j0ono0/handheld_game_console_prototype_01/arduino_game/resources.cpp

#include "resources.h"

const uint8_t terrain_1[] = {
	1, 1, 1, 1, 1, 1, 1, 1, 1, 1, 1, 1, 1, 1, 1, 1, 1, 1, 1, 1, 1, 1, 1, 1, 1, 1, 1, 1, 1, 1, 1, 1, 1, 1, 1, 1, 1, 1, 1, 1,
	1, 1, 1, 1, 1, 1, 1, 1, 1, 1, 1, 1, 1, 1, 1, 1, 1, 1, 1, 1, 1, 1, 1, 1, 1, 1, 1, 1, 1, 1, 1, 1, 1, 1, 1, 1, 1, 1, 1, 1,
	1, 1, 1, 1, 1, 1, 1, 1, 1, 1, 1, 1, 1, 1, 1, 1, 1, 1, 1, 1, 1, 1, 1, 1, 1, 1, 1, 1, 1, 1, 1, 1, 1, 1, 1, 1, 1, 1, 1, 1,
	1, 1, 1, 1, 1, 1, 1, 1, 1, 1, 1, 1, 1, 1, 1, 1, 1, 1, 1, 1, 1, 1, 1, 1, 1, 1, 1, 1, 1, 1, 1, 1, 1, 1, 1, 1, 1, 1, 1, 1,
	1, 1, 1, 1, 1, 1, 1, 1, 1, 1, 1, 1, 1, 1, 1, 1, 1, 1, 1, 1, 1, 1, 1, 1, 1, 1, 1, 1, 1, 1, 1, 1, 1, 1, 1, 1, 1, 1, 1, 1,
	1, 1, 1, 1, 1, 1, 1, 1, 1, 1, 1, 1, 1, 1, 1, 1, 1, 1, 1, 1, 1, 1, 1, 1, 1, 1, 1, 1, 1, 1, 1, 1, 1, 1, 1, 1, 1, 1, 1, 1,
	1, 1, 1, 1, 1, 1, 1, 1, 1, 1, 1, 1, 1, 1, 1, 1, 1, 1, 1, 1, 1, 1, 1, 1, 1, 1, 1, 1, 1, 1, 1, 1, 1, 1, 1, 1, 1, 1, 1, 1,
	1, 1, 1, 1, 1, 1, 1, 1, 1, 1, 1, 1, 1, 1, 1, 1, 1, 1, 1, 1, 1, 1, 1, 1, 1, 1, 1, 1, 1, 1, 1, 1, 1, 1, 1, 1, 1, 1, 1, 1,
	1, 1, 1, 1, 1, 1, 1, 1, 1, 1, 1, 28, 34, 34, 34, 34, 34, 34, 34, 34, 24, 1, 1, 1, 1, 1, 1, 28, 34, 34, 34, 34, 34, 34, 24, 1, 1, 1, 1, 1,
	1, 1, 1, 1, 1, 1, 1, 1, 1, 1, 1, 28, 13, 13, 13, 13, 13, 13, 13, 13, 29, 1, 1, 1, 1, 1, 1, 28, 13, 13, 13, 13, 13, 13, 29, 1, 1, 1, 1, 1,
	1, 1, 1, 1, 1, 1, 1, 1, 1, 1, 1, 28, 13, 13, 13, 13, 13, 13, 13, 13, 29, 1, 1, 28, 34, 34, 34, 33, 13, 13, 13, 13, 13, 13, 29, 1, 1, 1, 1, 1,
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
	1, 1, 1, 1, 1, 1, 1, 1, 
	1, 1, 1, 1, 1, 1, 1, 1, 
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
};


const Entity entities_01[] = {
    {plr_t, 16, 6, 2, 0, 0, &plr_behaviour, &sprite_prof_stationary_west},
    // {officer_t, 8, 8, 2, 0, 0, NULL , NULL},
    {office_chair_t, 7, 7, 2, 0, 0, NULL , &sprite_office_chair},

    // {desktop_terminal_t, 12, 7, 4, 0, 0, NULL , &sprite_desktop_terminal},
    {dotpanel_right_t, 13, 9, 4, 0, 0, NULL , &sprite_desktop_panel},
    {inbuilt_terminal_t, 14, 8, 4, 0, 0, NULL , &sprite_inbuilt_terminal},
    {desk_clutter_t, 13, 8, 4, 0, 0, NULL , &sprite_desktop_clutter},

    {target_t, 12, 7, 1, 0, 0, NULL, &sprite_target},
    {target_t, 16, 8, 1, 0, 0, NULL, &sprite_target},
    {target_t, 12, 9, 1, 0, 0, NULL, &sprite_target},
    {target_t, 15, 10, 1, 0, 0, NULL, &sprite_target},
    {target_t, 14, 11, 1, 0, 0, NULL, &sprite_target},
    {target_t, 17, 11, 1, 0, 0, NULL, &sprite_target},
    {target_t, 15, 12, 1, 0, 0, NULL, &sprite_target},

    {crate_t, 15, 7, 2, 0, 0, &crate_behaviour, &sprite_crate},
    {crate_t, 15, 8, 2, 0, 0, &crate_behaviour, &sprite_crate},
    {crate_t, 15, 9, 2, 0, 0, &crate_behaviour, &sprite_crate},
    {crate_t, 12, 11, 2, 0, 0, &crate_behaviour, &sprite_crate},
    {crate_t, 14, 11, 2, 0, 0, &crate_behaviour, &sprite_crate},
    {crate_t, 15, 11, 2, 0, 0, &crate_behaviour, &sprite_crate},
    {crate_t, 16, 11, 2, 0, 0, &crate_behaviour, &sprite_crate},
};

const Entity entities_02[] = {
    {plr_t, 6, 7, 2, 0, 0, &plr_behaviour, &sprite_prof_stationary_east},
    {strongman_t, 11, 10, 2, 0, 0, NULL, &sprite_strongman},
    {office_chair_t,  11, 8, 2, 0, 0, NULL , &sprite_office_chair},
    {powerconverter_t, 4, 11, 2, 0, 0, &powerconverter_behaviour, &sprite_powerconverter},
    {powerconverter_t, 8, 8, 2, 0, 0, &powerconverter_behaviour, &sprite_powerconverter},
    {powerconverter_t, 7, 12, 2, 0, 0, &powerconverter_behaviour, &sprite_powerconverter},
    {powerconverter_t, 10, 13, 2, 0, 0, &powerconverter_behaviour, &sprite_powerconverter},
    {target_t, 6, 11, 1, 0, 0, NULL, &sprite_target},
    {target_t, 6, 12, 1, 0, 0, NULL, &sprite_target},
    {target_t, 6, 13, 1, 0, 0, NULL, &sprite_target},
};

const Entity entities_03[] = {
    {plr_t, 10, 5, 2, 0, 0, &plr_behaviour, &sprite_prof_stationary_east},
    {strongman_t, 11, 6, 2, 0, 0, NULL, &sprite_strongman},
    {office_chair_t,  14, 10, 2, 0, 0, NULL , &sprite_office_chair},
    {crate_t, 6, 6, 2, 0, 0, &crate_behaviour, &sprite_crate},
    {crate_t, 5, 10, 2, 0, 0, &crate_behaviour, &sprite_crate},
    {target_t, 3, 6, 1, 0, 0, NULL, &sprite_target},
    {target_t, 5, 6, 1, 0, 0, NULL, &sprite_target}
};


// Collate all terrains and entities
const EnvSpec environmentList[] = {
    {terrain_1, 0, entities_01, 1, sizeof(entities_01) / sizeof(Entity)},
    {terrain_2, 10, entities_02, 2, sizeof(entities_02) / sizeof(Entity)},
    {terrain_3, 20, entities_03, 2, sizeof(entities_03) / sizeof(Entity)},
};
