j0ono0/handheld_game_console_prototype_01/arduino_game/sprites_entities.c

#include <avr/pgmspace.h>
#include <inttypes.h>
#include "customtypes.h"

const uint16_t sprite_data_target[] PROGMEM = {

	0x7e0, 0x7e0, 0xd924, 0xd924, 0x7e0, 0xd924, 0xd924, 0x7e0, 0xd924, 0xd924, 0x7e0, 0xd924, 0x7e0, 0xd924, 0x7e0, 0x7e0, 
	0x7e0, 0xd924, 0xd924, 0x7e0, 0x7e0, 0x7e0, 0x7e0, 0x7e0, 0x7e0, 0x7e0, 0x7e0, 0x7e0, 0x7e0, 0xd924, 0xd924, 0x7e0, 
	0x7e0, 0x7e0, 0x7e0, 0xd924, 0x7e0, 0x7e0, 0x7e0, 0x7e0, 0x7e0, 0x7e0, 0x7e0, 0x7e0, 0xd924, 0x7e0, 0xd924, 0x7e0, 
	0x7e0, 0xd924, 0x7e0, 0x7e0, 0xd924, 0x7e0, 0x7e0, 0x7e0, 0x7e0, 0x7e0, 0x7e0, 0xd924, 0x7e0, 0x7e0, 0x7e0, 0x7e0, 
	0x7e0, 0x7e0, 0x7e0, 0x7e0, 0x7e0, 0xd924, 0x7e0, 0x7e0, 0x7e0, 0x7e0, 0xd924, 0x7e0, 0x7e0, 0x7e0, 0xd924, 0x7e0, 
	0x7e0, 0xd924, 0x7e0, 0x7e0, 0x7e0, 0x7e0, 0xd924, 0x7e0, 0x7e0, 0xd924, 0x7e0, 0x7e0, 0x7e0, 0x7e0, 0xd924, 0x7e0, 
	0x7e0, 0xd924, 0x7e0, 0x7e0, 0x7e0, 0x7e0, 0x7e0, 0xd924, 0xd924, 0x7e0, 0x7e0, 0x7e0, 0x7e0, 0x7e0, 0x7e0, 0x7e0, 
	0x7e0, 0x7e0, 0x7e0, 0x7e0, 0x7e0, 0x7e0, 0xd924, 0x7e0, 0x7e0, 0xd924, 0x7e0, 0x7e0, 0x7e0, 0x7e0, 0xd924, 0x7e0, 
	0x7e0, 0xd924, 0x7e0, 0x7e0, 0x7e0, 0xd924, 0x7e0, 0x7e0, 0x7e0, 0x7e0, 0xd924, 0x7e0, 0x7e0, 0x7e0, 0xd924, 0x7e0, 
	0x7e0, 0xd924, 0x7e0, 0x7e0, 0xd924, 0x7e0, 0x7e0, 0x7e0, 0x7e0, 0x7e0, 0x7e0, 0xd924, 0x7e0, 0x7e0, 0x7e0, 0x7e0, 
	0x7e0, 0x7e0, 0x7e0, 0xd924, 0x7e0, 0x7e0, 0x7e0, 0x7e0, 0x7e0, 0x7e0, 0x7e0, 0x7e0, 0xd924, 0x7e0, 0xd924, 0x7e0, 
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
	0x7e0, 0x7e0, 0x7e0, 0x7e0, 0x7e0, 0x7e0, 0x7e0, 0x7e0, 0x7e0, 0x1083, 0x92cb, 0x92cb, 0x1083, 0x7e0, 0x7e0, 0x7e0, 
	0x7e0, 0x7e0, 0x7e0, 0x7e0, 0x7e0, 0x7e0, 0x7e0, 0x7e0, 0x7e0, 0x1083, 0x73ae, 0x73ae, 0x1083, 0x7e0, 0x7e0, 0x7e0, 
};

const SpriteFrame sprite_frame_target PROGMEM = { 16, 13, sprite_data_target };
const SpriteFrame sprite_frame_crate PROGMEM = { 16, 23, sprite_data_crate };
const SpriteFrame sprite_frame_crate_active PROGMEM = { 16, 23, sprite_data_crate_active };
const SpriteFrame sprite_frame_powerconverter PROGMEM = { 16, 25, sprite_data_powerconverter };
const SpriteFrame sprite_frame_powerconverter_active PROGMEM = { 16, 25, sprite_data_powerconverter_active };
const SpriteFrame sprite_frame_prof_stationary_west PROGMEM = { 16, 32, sprite_data_prof_stationary_west };
const SpriteFrame sprite_frame_prof_stationary_east PROGMEM = { 16, 32, sprite_data_prof_stationary_east };
const SpriteFrame sprite_frame_prof_walk_east_1 PROGMEM = { 16, 32, sprite_data_prof_walk_east_1 };
const SpriteFrame sprite_frame_prof_walk_east_2 PROGMEM = { 16, 32, sprite_data_prof_walk_east_2 };
const SpriteFrame sprite_frame_prof_walk_west_1 PROGMEM = { 16, 32, sprite_data_prof_walk_west_1 };
const SpriteFrame sprite_frame_prof_walk_west_2 PROGMEM = { 16, 32, sprite_data_prof_walk_west_2 };
const SpriteFrame sprite_frame_prof_walk_south_1 PROGMEM = { 16, 32, sprite_data_prof_walk_south_1 };
const SpriteFrame sprite_frame_prof_walk_south_2 PROGMEM = { 16, 32, sprite_data_prof_walk_south_2 };
const SpriteFrame sprite_frame_prof_walk_north_1 PROGMEM = { 16, 32, sprite_data_prof_walk_north_1 };
const SpriteFrame sprite_frame_prof_walk_north_2 PROGMEM = { 16, 32, sprite_data_prof_walk_north_2 };


//////////////////////////////////////////////////////
// NOTE: ALL BELOW IS HAND CODED
// everything above is generated by a script

// Framesets /////////////////////////////////////////////////////////////////

const SpriteFrame *sprite_frameset_prof_stationary_west[] = {&sprite_frame_prof_stationary_west};
const SpriteFrame *sprite_frameset_prof_stationary_east[] = {&sprite_frame_prof_stationary_east};
const SpriteFrame *sprite_frameset_target[] = {&sprite_frame_target};
const SpriteFrame *sprite_frameset_crate[] = {&sprite_frame_crate};
const SpriteFrame *sprite_frameset_crate_active[] = {&sprite_frame_crate_active};
const SpriteFrame *sprite_frameset_powerconverter[] = {&sprite_frame_powerconverter};
const SpriteFrame *sprite_frameset_powerconverter_active[] = {&sprite_frame_powerconverter_active};

const SpriteFrame *sprite_frameset_prof_walk_north[] = {&sprite_frame_prof_walk_north_1, &sprite_frame_prof_walk_north_2};
const SpriteFrame *sprite_frameset_prof_walk_east[] = {&sprite_frame_prof_walk_east_1, &sprite_frame_prof_walk_east_2};
const SpriteFrame *sprite_frameset_prof_walk_south[] = {&sprite_frame_prof_walk_south_1, &sprite_frame_prof_walk_south_2};
const SpriteFrame *sprite_frameset_prof_walk_west[] = {&sprite_frame_prof_walk_west_1, &sprite_frame_prof_walk_west_2};

// Sprites /////////////////////////////////////////////////////////////////

const Sprite sprite_prof_walk_north = {2, sprite_frameset_prof_walk_north};
const Sprite sprite_prof_walk_east = {2, sprite_frameset_prof_walk_east};
const Sprite sprite_prof_walk_south = {2, sprite_frameset_prof_walk_south};
const Sprite sprite_prof_walk_west = {2, sprite_frameset_prof_walk_west};
const Sprite sprite_prof_stationary_west = {1, sprite_frameset_prof_stationary_west };
const Sprite sprite_prof_stationary_east = {1, sprite_frameset_prof_stationary_east };

const Sprite sprite_target = {1, sprite_frameset_target };
const Sprite sprite_crate = {1, sprite_frameset_crate };
const Sprite sprite_crate_active = {1, sprite_frameset_crate_active};
const Sprite sprite_powerconverter = {1, sprite_frameset_powerconverter};
const Sprite sprite_powerconverter_active = {1, sprite_frameset_powerconverter_active};
