j0ono0/handheld_game_console_prototype_01/arduino_game/sprites.h

#ifndef game_sprite_assets_h
#define game_sprite_assets_h


#include "customtypes.h"



extern const Sprite sprite_prof_walk_north;
extern const Sprite sprite_prof_walk_east;
extern const Sprite sprite_prof_walk_south;
extern const Sprite sprite_prof_walk_west;
extern const Sprite sprite_prof_stationary_west;
extern const Sprite sprite_prof_stationary_east;

extern const Sprite sprite_target;
extern const Sprite sprite_crate;
extern const Sprite sprite_crate_active;
extern const Sprite sprite_powerconverter;
extern const Sprite sprite_powerconverter_active;

extern const Sprite sprite_strongman;
extern const Sprite sprite_office_chair;
extern const Sprite sprite_desktop_panel;
extern const Sprite sprite_desktop_terminal;
extern const Sprite sprite_inbuilt_terminal;
extern const Sprite sprite_desktop_clutter;

// Testing animation speeds
extern const Sprite sprite_crate_1;
extern const Sprite sprite_crate_2;
extern const Sprite sprite_crate_3;
extern const Sprite sprite_crate_4;
extern const Sprite sprite_crate_5;
extern const Sprite sprite_crate_6;

#endif
