j0ono0/handheld_game_console_prototype_01/arduino_game/behaviours.h

#ifndef game_behaviours_h
#define game_behaviours_h

//////////////////////////////////////////////////////////////////
//
// functions assigned to individual instances of Entities
//
//////////////////////////////////////////////////////////////////

#include "Arduino.h"
#include "customtypes.h"
#include "interactions.h"
#include "sprites.h"
#include "input.h"

void updateMovementTransition(Entity *e, uint8_t step_distance);
void do_nothing(Entity *self, GameManager *gm);
void crate_behaviour(Entity *self, GameManager *gm);
void powerconverter_behaviour(Entity *self, GameManager *gm);
void plr_behaviour(Entity *self, GameManager *gm);


#endif
