j0ono0/handheld_game_console_prototype_01/arduino_game/resources.h

#ifndef game_resources_h
#define game_resources_h

#include <stddef.h>
#include "customtypes.h"
#include "behaviours.h"
#include "sprites.h"

extern const uint8_t terrain_tiles_indexed[];
extern const EnvSpec environmentList[];


#endif
